piwicode/bandoneon/datasheets/CM-M1-6-M2-M2-5-M3-figur-M5-M6-M8-304-A2-70-En-Acier.jpg_.webp

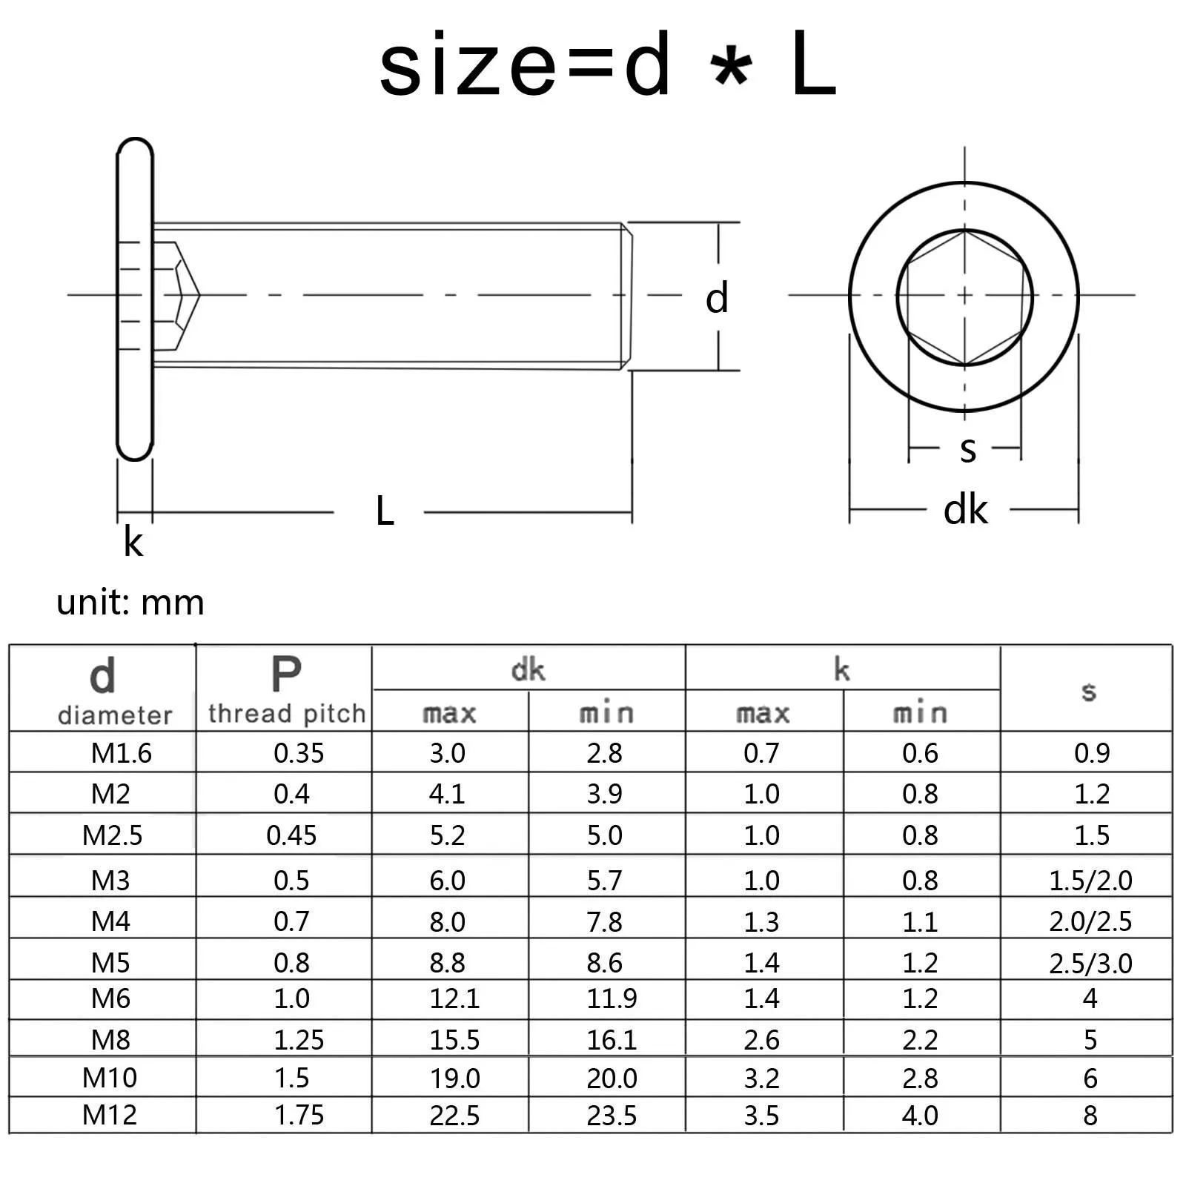
datasheets/CM-M1-6-M2-M2-5-M3-figur-M5-M6-M8-304-A2-70-En-Acier.jpg_.webp
