piwicode/bandoneon/datasheets/jack.webp

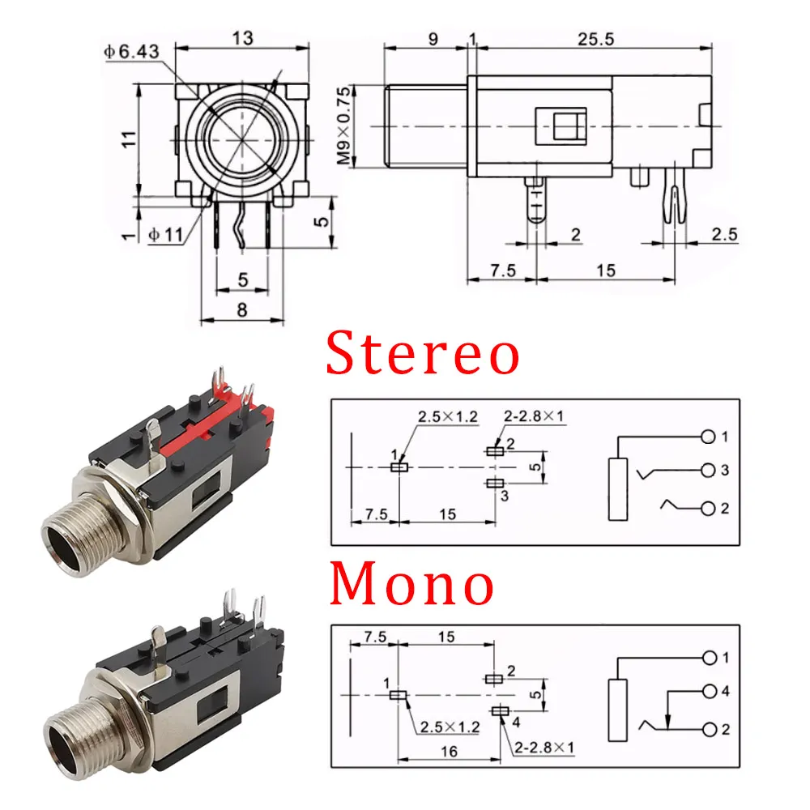
datasheets/jack.webp
