piwicode/bandoneon/images/Screenshot 2024-01-19 135625.png

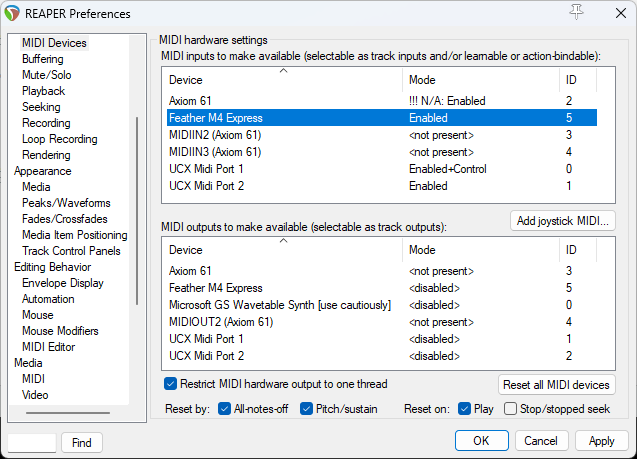
images/Screenshot 2024-01-19 135625.png
