piwicode/bandoneon/images/Screenshot 2024-01-19 135826.png

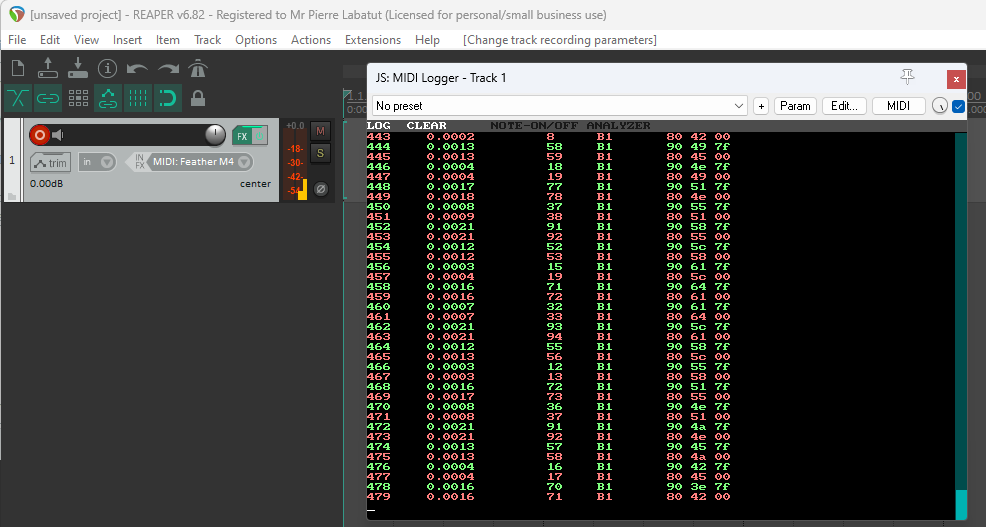
images/Screenshot 2024-01-19 135826.png
