piwicode/bandoneon/images/Screenshot 2024-01-19 183334.png

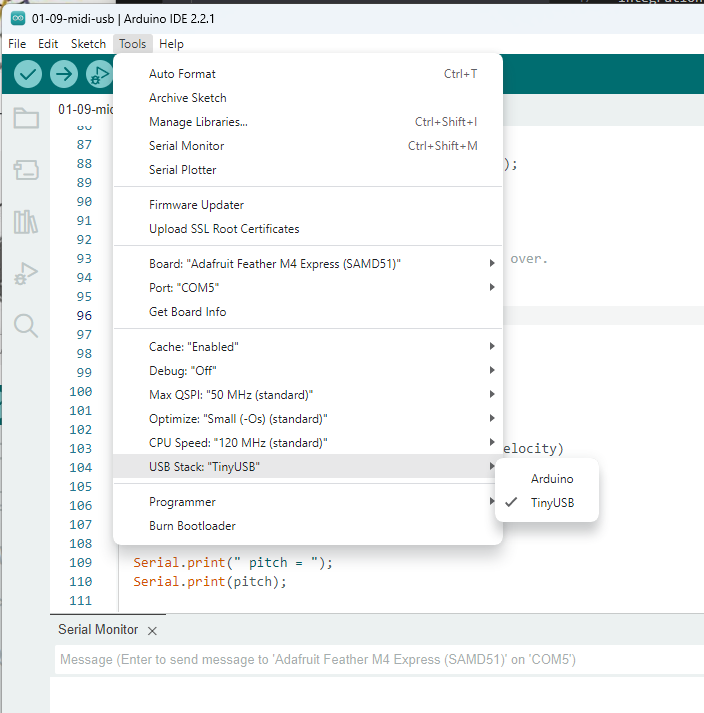
images/Screenshot 2024-01-19 183334.png
