piwicode/bandoneon/images/Screenshot 2024-01-19 212708.jpg

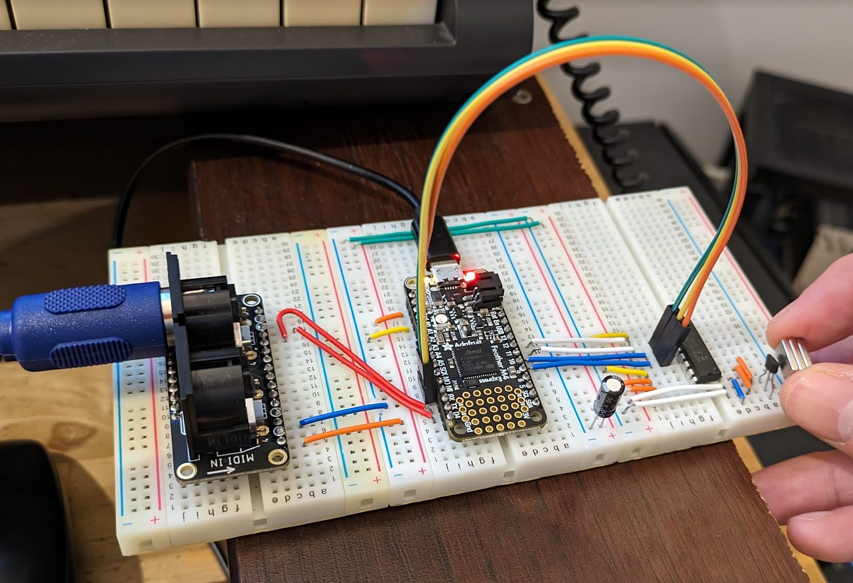
images/Screenshot 2024-01-19 212708.jpg
