piwicode/bandoneon/images/Screenshot 2024-01-24 084300.png

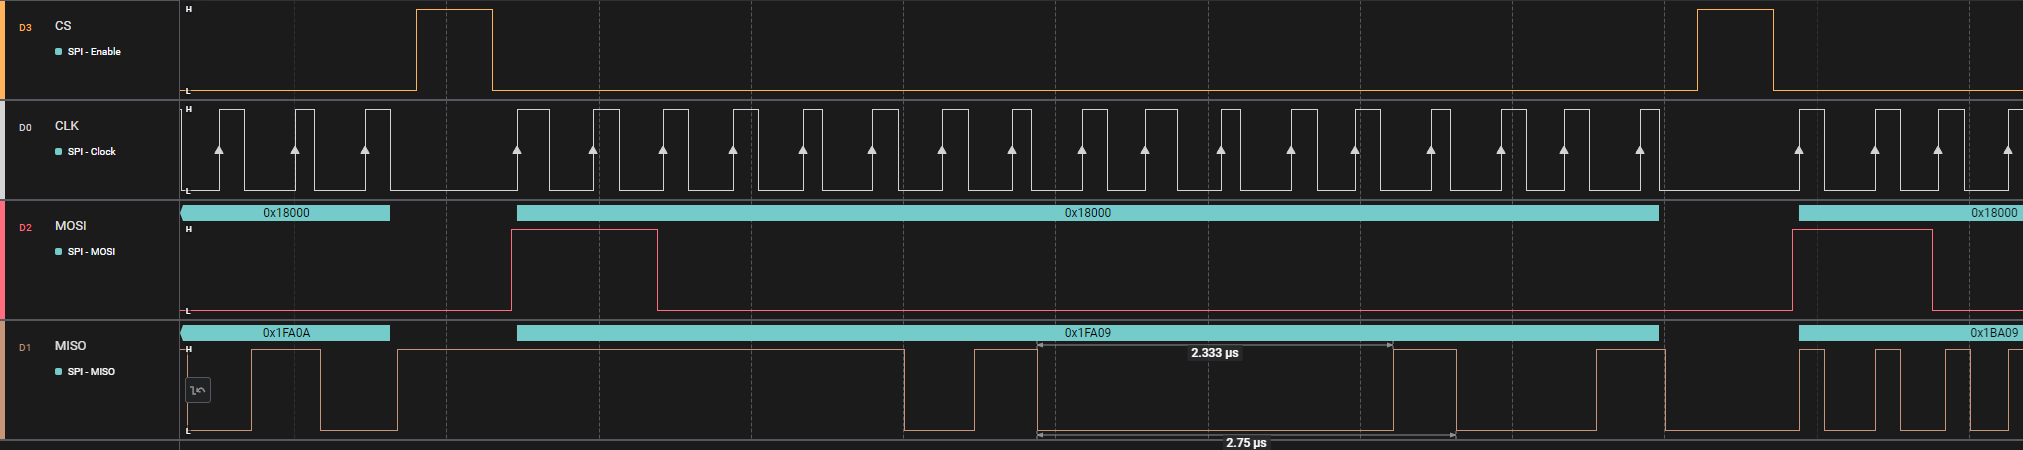
images/Screenshot 2024-01-24 084300.png
