piwicode/bandoneon/images/Screenshot 2024-01-25 232503.png

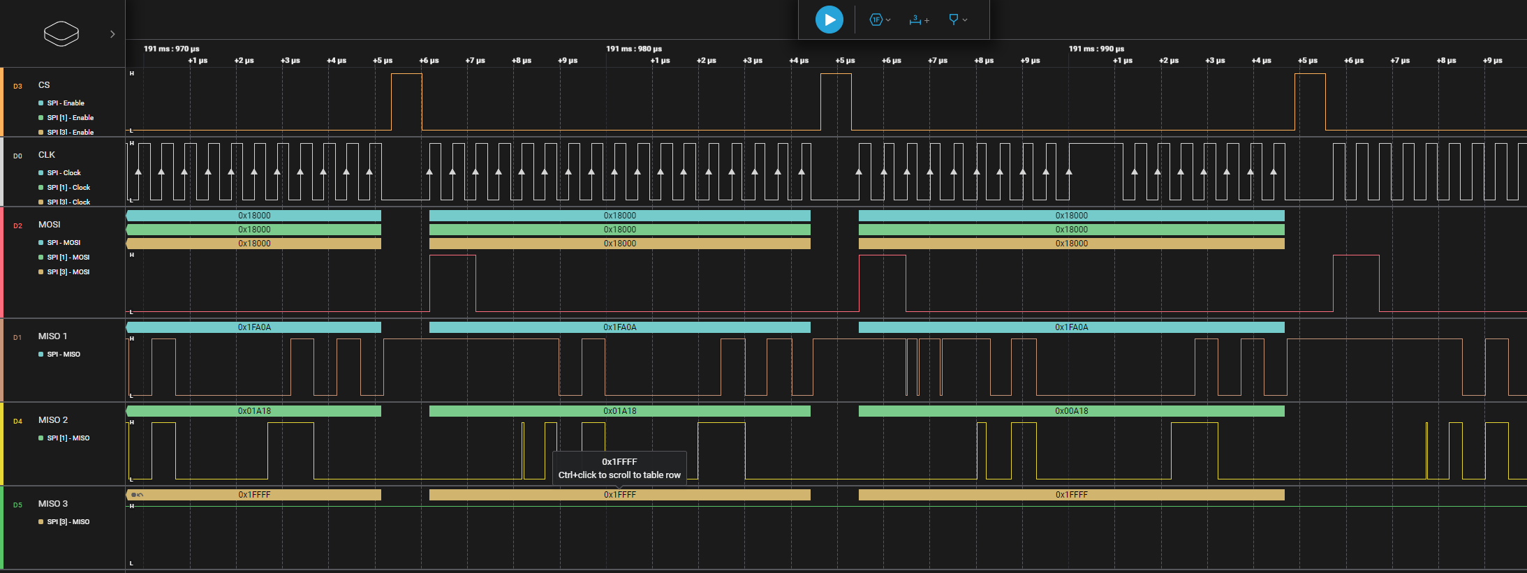
images/Screenshot 2024-01-25 232503.png
