piwicode/bandoneon/images/Screenshot 2024-01-27 221911.png

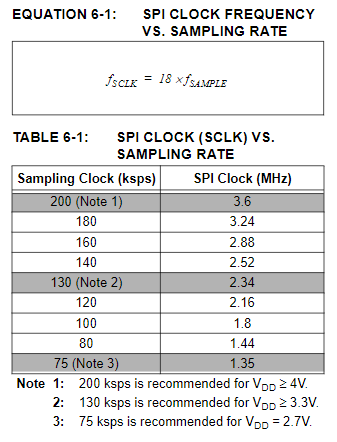
images/Screenshot 2024-01-27 221911.png
