piwicode/bandoneon/images/Screenshot 2024-01-31 140824.png

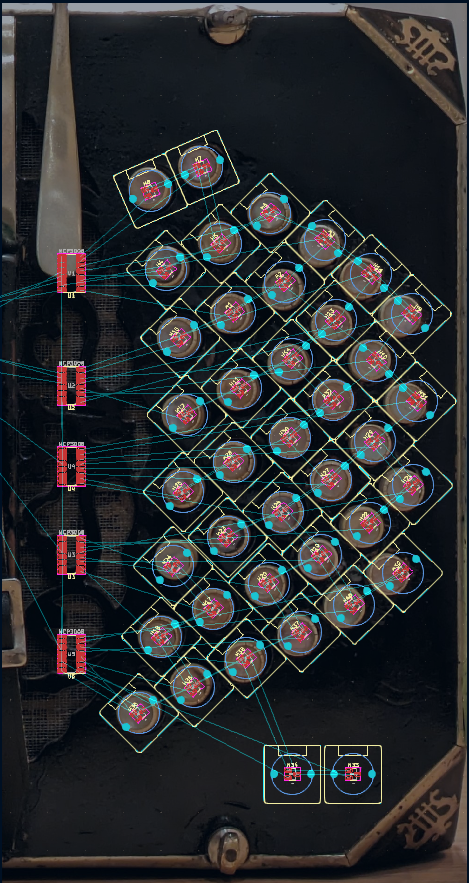
images/Screenshot 2024-01-31 140824.png
