piwicode/bandoneon/images/Screenshot 2024-01-31 140842.png

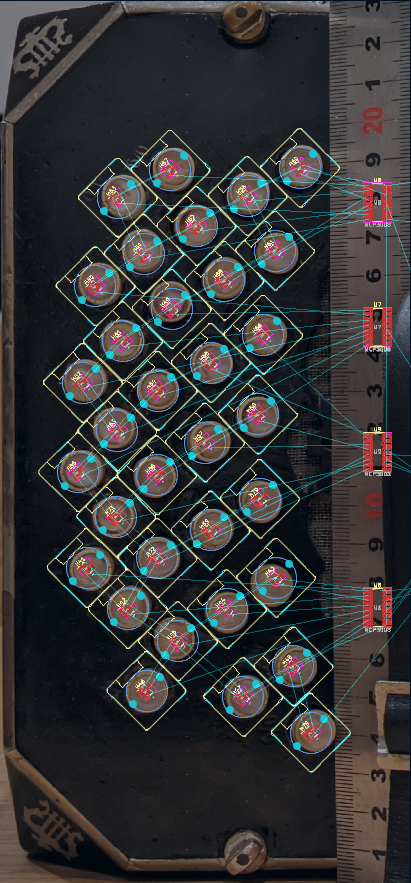
images/Screenshot 2024-01-31 140842.png
