piwicode/bandoneon/images/Screenshot 2024-01-31 201740.png

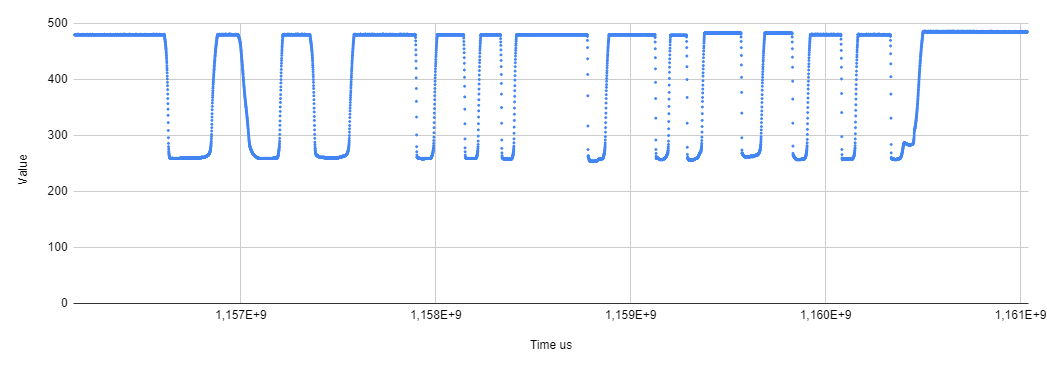
images/Screenshot 2024-01-31 201740.png
