piwicode/bandoneon/images/Screenshot 2024-02-16 172553.png

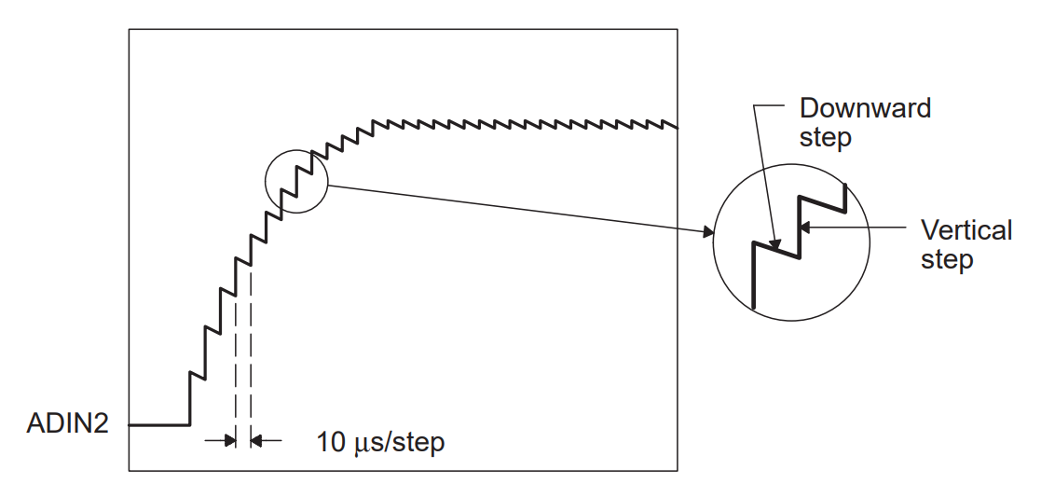
images/Screenshot 2024-02-16 172553.png
