piwicode/bandoneon/images/Screenshot 2024-02-16 174339.png

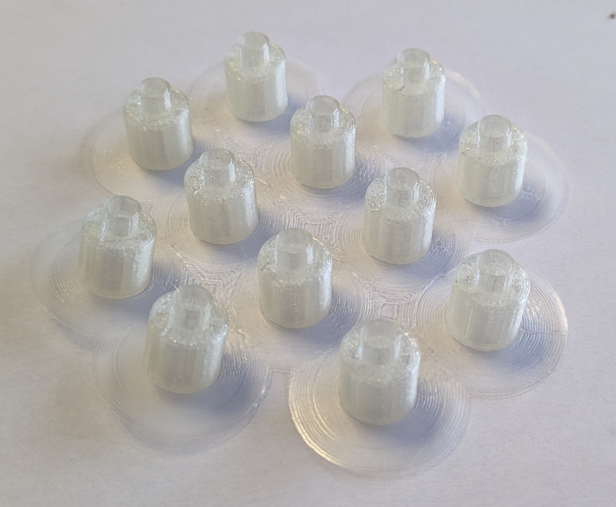
images/Screenshot 2024-02-16 174339.png
