piwicode/bandoneon/images/Screenshot 2024-02-16 190442.png

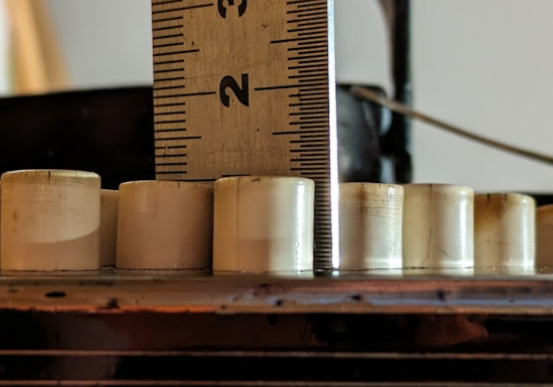
images/Screenshot 2024-02-16 190442.png
