piwicode/bandoneon/images/Screenshot 2024-02-16 225610.png

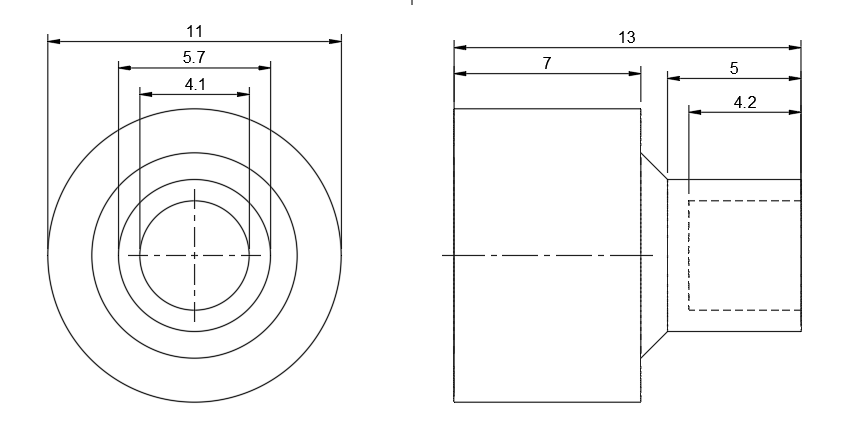
images/Screenshot 2024-02-16 225610.png
