piwicode/bandoneon/images/Screenshot 2024-02-16 225720.png

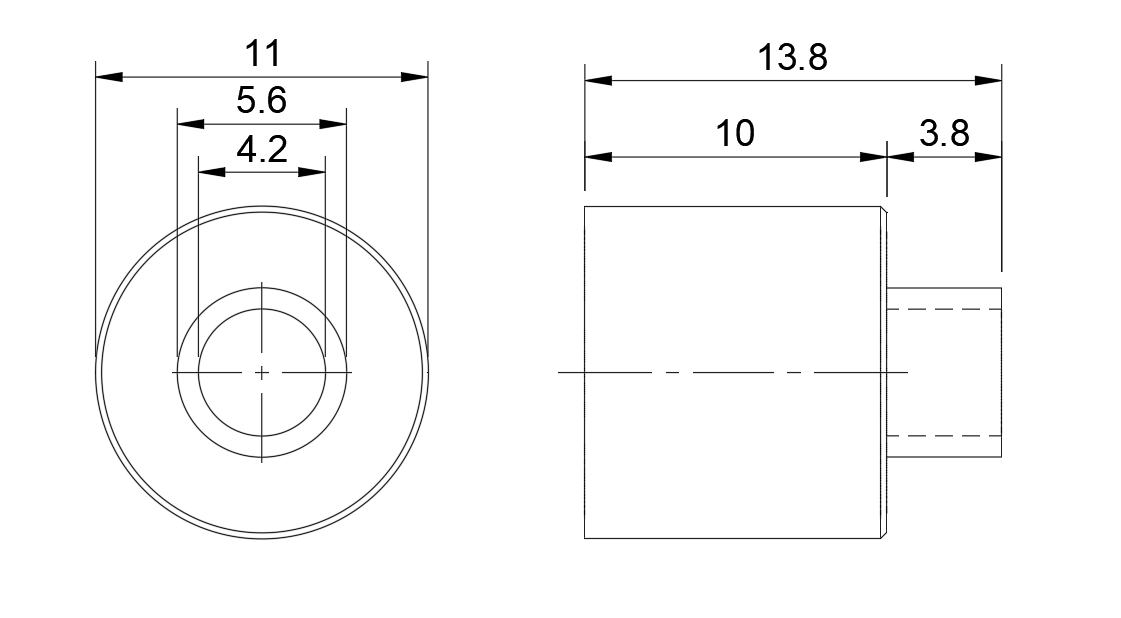
images/Screenshot 2024-02-16 225720.png
