piwicode/bandoneon/images/Screenshot 2024-02-16 230251.png

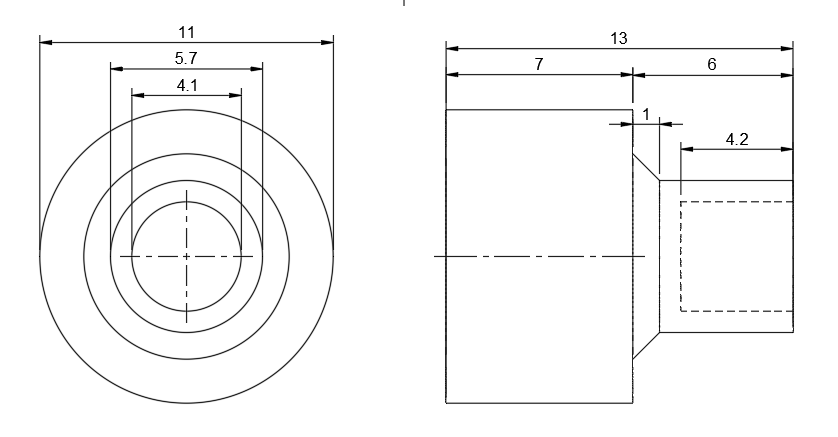
images/Screenshot 2024-02-16 230251.png
