piwicode/bandoneon/images/Screenshot 2024-03-01 095530.png

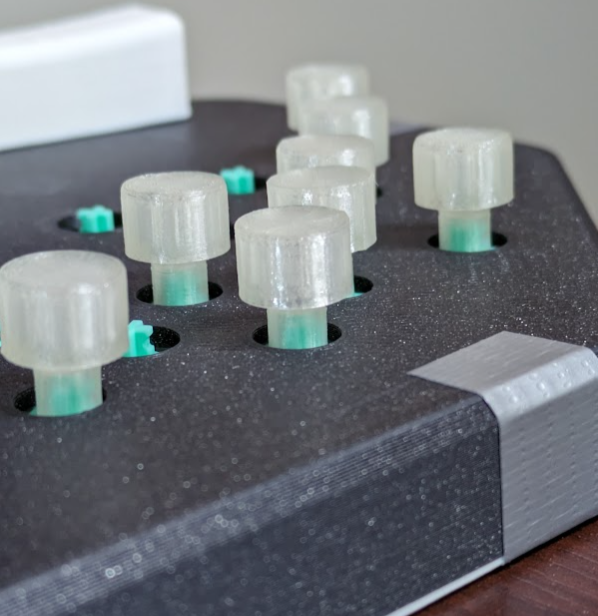
images/Screenshot 2024-03-01 095530.png
