piwicode/bandoneon/images/Screenshot 2024-03-01 095839.png

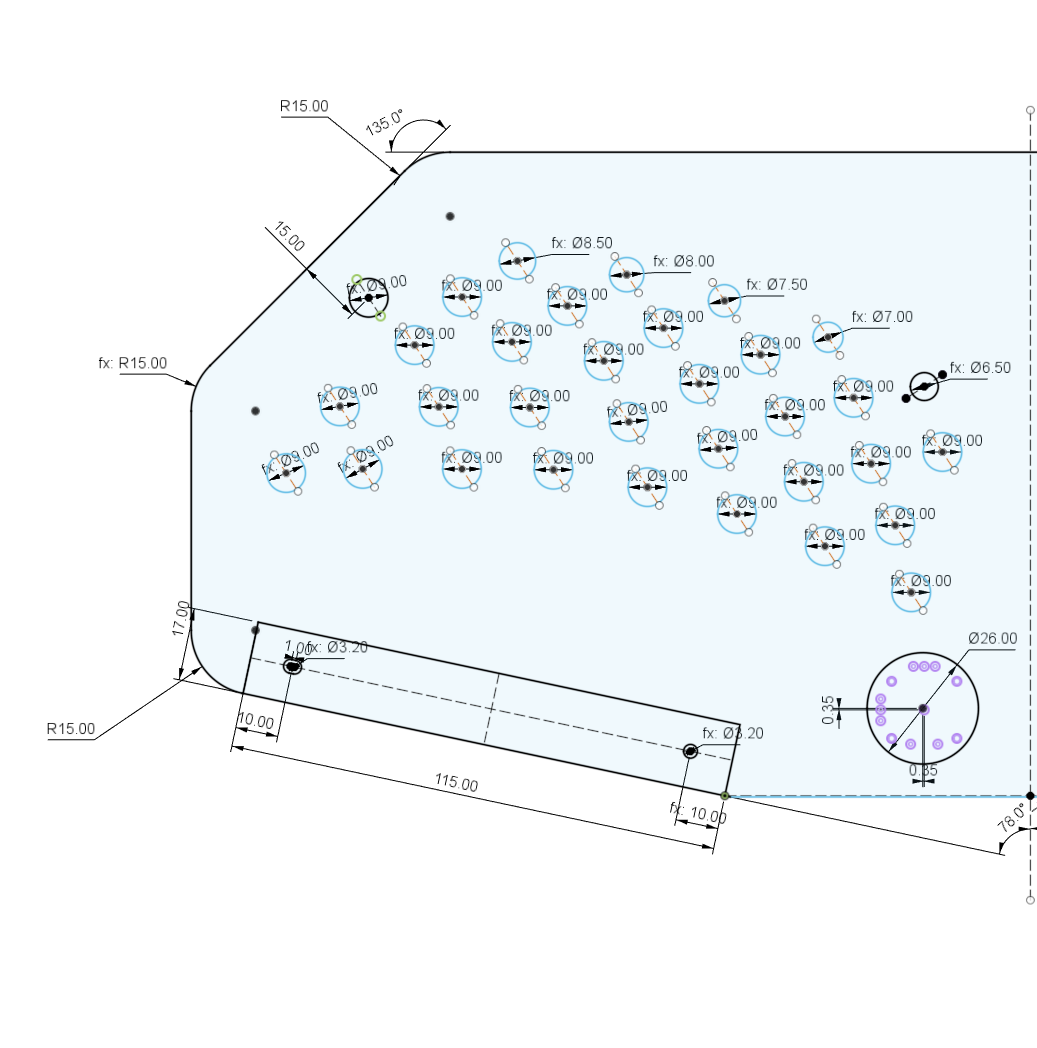
images/Screenshot 2024-03-01 095839.png
