piwicode/bandoneon/images/Screenshot 2024-04-13 213430.png

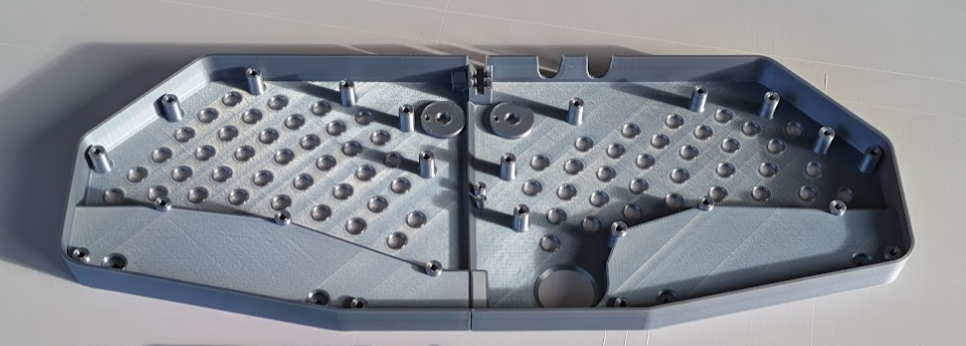
images/Screenshot 2024-04-13 213430.png
