piwicode/bandoneon/images/Screenshot 2024-04-13 214124.png

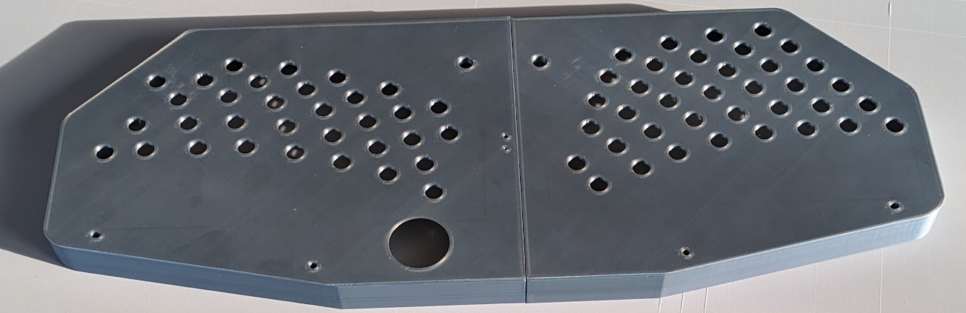
images/Screenshot 2024-04-13 214124.png
