piwicode/bandoneon/images/Screenshot 2024-04-13 214628.png

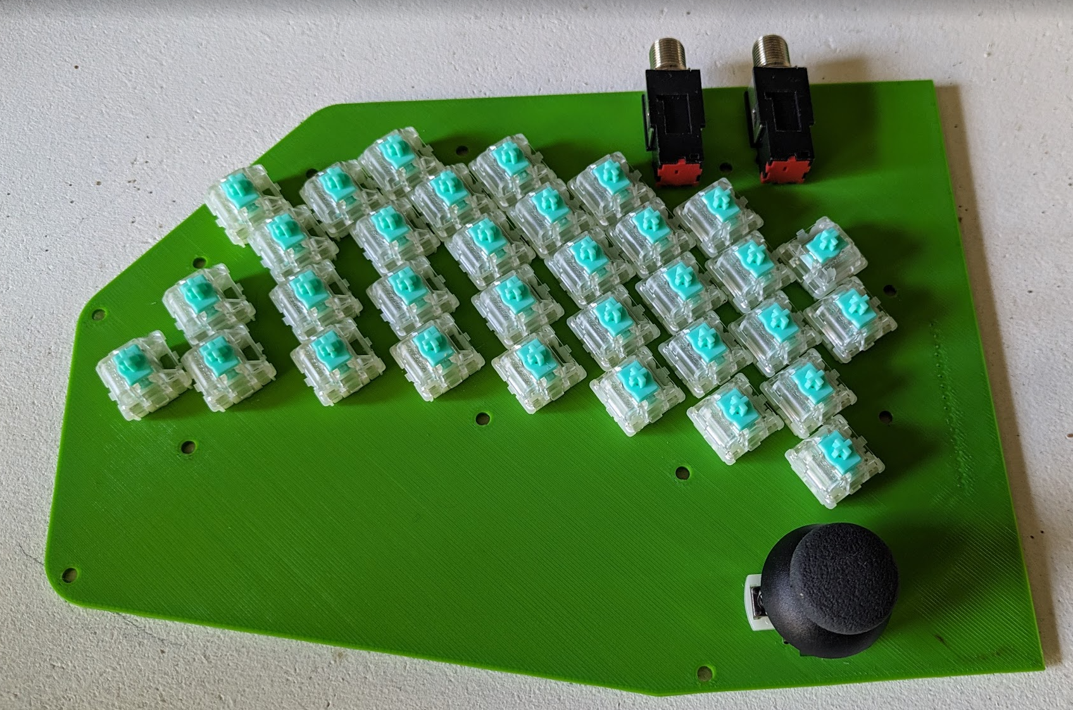
images/Screenshot 2024-04-13 214628.png
