piwicode/bandoneon/images/Screenshot from 2024-02-16 18-17-40.png

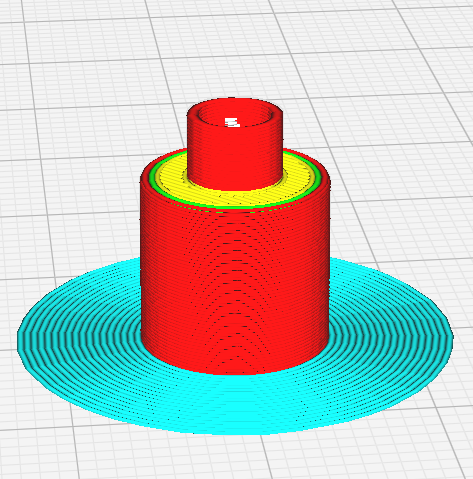
images/Screenshot from 2024-02-16 18-17-40.png
