piwicode/bandoneon/layout/half_left_side.jpg

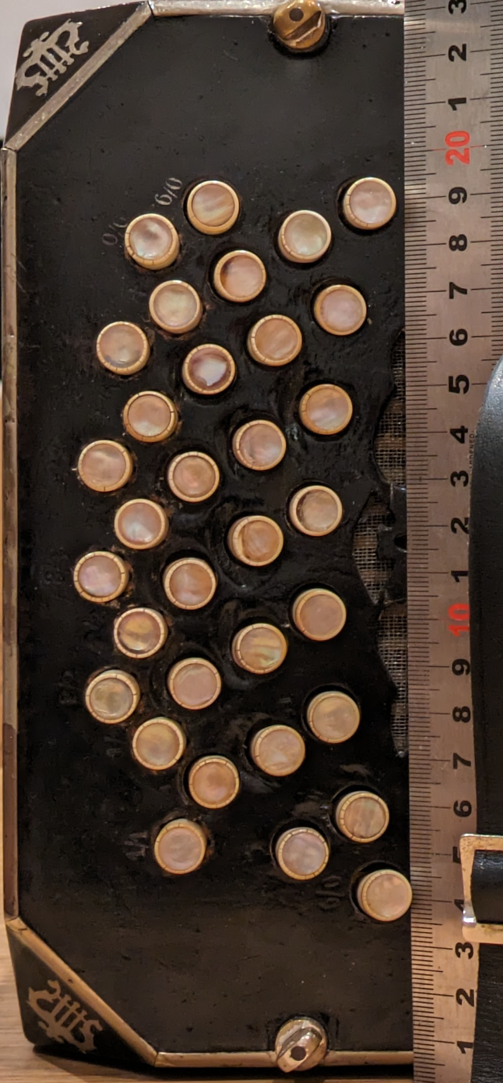
layout/half_left_side.jpg
