piwicode/bandoneon/layout/half_right_side.jpg

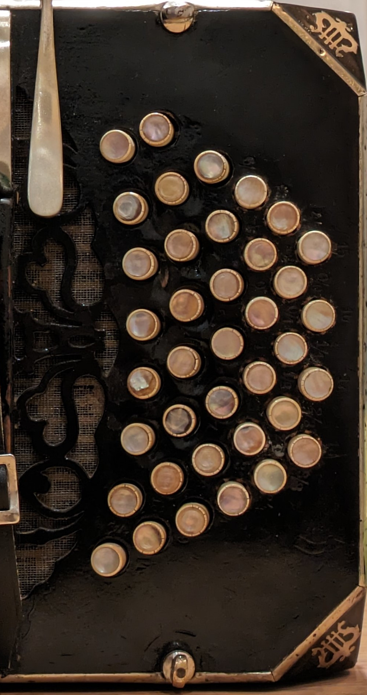
layout/half_right_side.jpg
