piwicode/bandoneon/layout/left_side.jpg

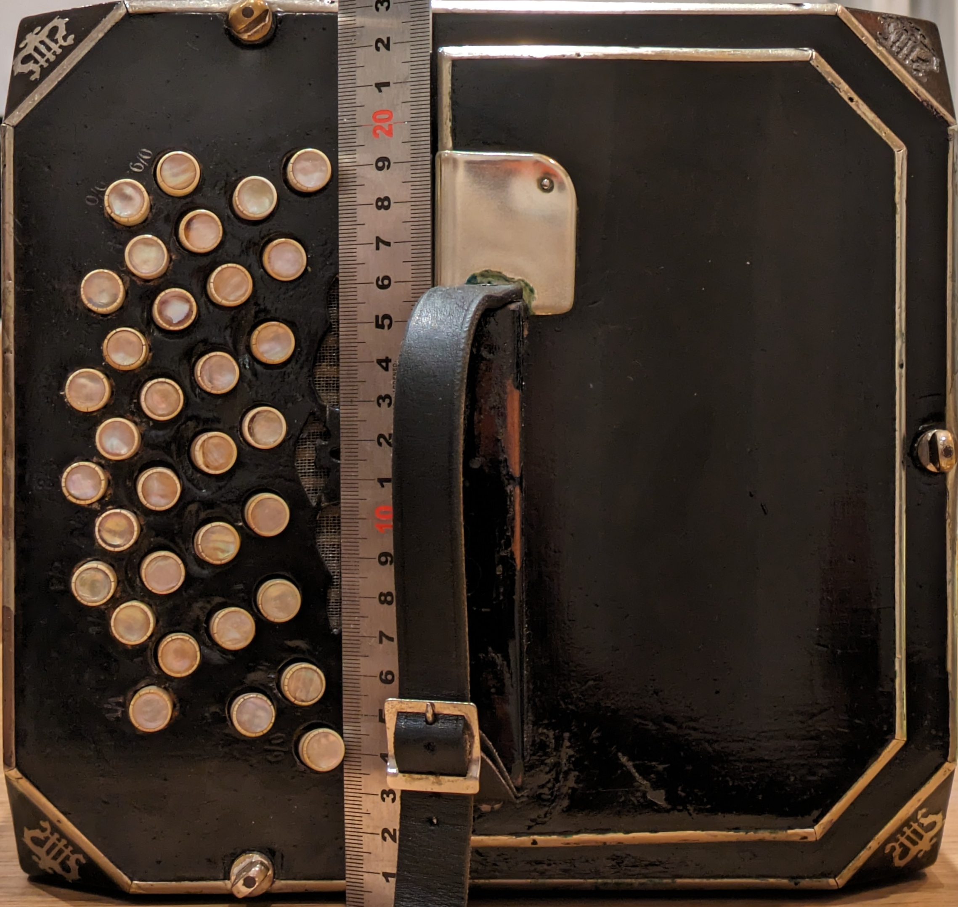
layout/left_side.jpg
