piwicode/bandoneon/layout/right_side.jpg

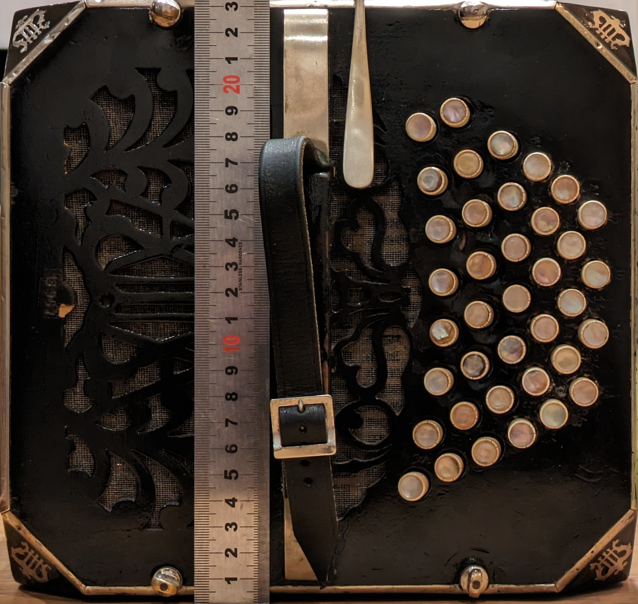
layout/right_side.jpg
