piwicode/bandoneon/stl/PCB R.stl

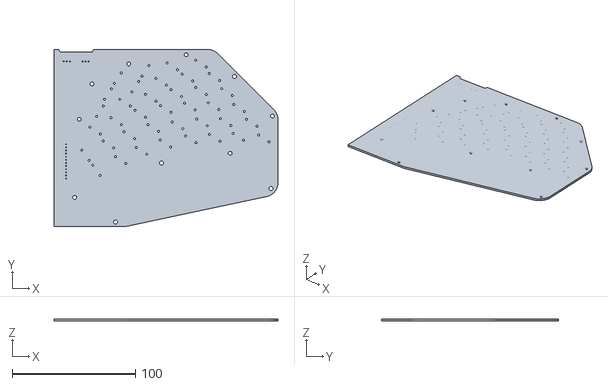
[picture p52: CAD file, 2024-03-18]
stl/PCB R.stl
182.0 x 143.8 x 1.60
