piwicode/bandoneon/boards/bandoneon/bandoneon.kicad_sch

## KiCad design boards/bandoneon/bandoneon.kicad_sch (2024-03-30)

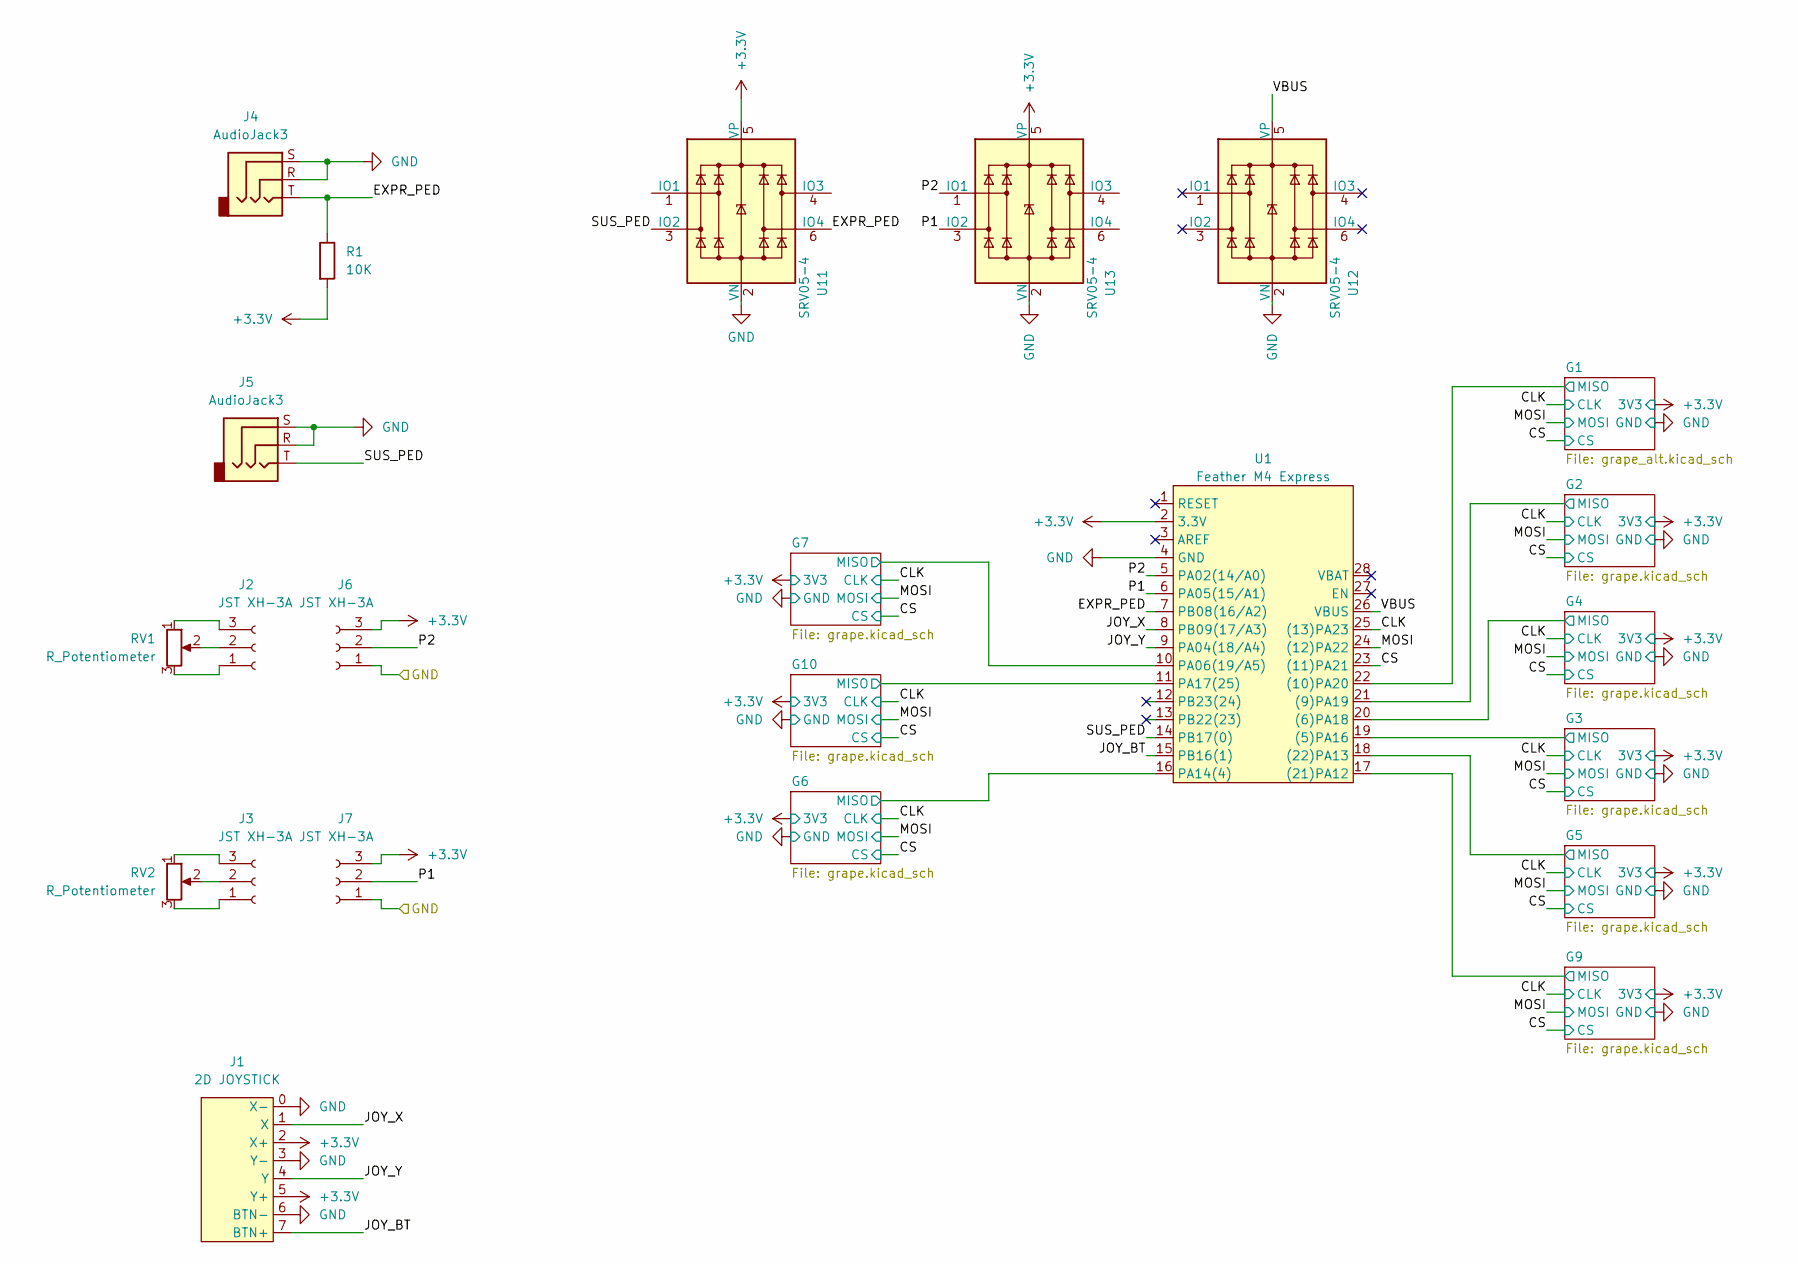
[picture p54: schematic bandoneon.kicad_sch]

Parts:
J1: 2D JOYSTICK; Adafruit (512) Analog 2-axis Thumb Joystick with Select But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
J2, J3: JST XH-3A
J4, J5: AudioJack3; Jack TRS
J6, J7: JST XH-3A; JST_XH_B3B-XH-A_1x03_P2.50mm_Vertical
R1: 10K; R_0603_1608Metric; LCSC Part C25804
RV1, RV2: R_Potentiometer
U1: Feather M4 Express; Adafruit_Feather_M4_Express
U11, U12, U13: SRV05-4; SOT-23-6; LCSC Part C2836319

Connections:
+3.3V: J1.2 (X+), J1.5 (Y+), J6.3, J7.3, R1.2, U1.2 (3.3V), U11.5 (VP), U13.5 (VP)
CLK: U1.25 ((13)PA23)
CS: U1.23 ((11)PA21)
EXPR_PED: J4.T, R1.1, U1.7 (PB08(16/A2)), U11.6 (IO4)
GND: J1.0 (X-), J1.3 (Y-), J1.6 (BTN-), J4.R, J4.S, J5.R, J5.S, J6.1, J7.1, U1.4 (GND), U11.2 (VN), U12.2 (VN), U13.2 (VN)
JOY_BT: J1.7 (BTN+), U1.15 (PB16(1))
JOY_X: J1.1 (X), U1.8 (PB09(17/A3))
JOY_Y: J1.4 (Y), U1.9 (PA04(18/A4))
MISO: U1.10 (PA06(19/A5)), U1.11 (PA17(25)), U1.16 (PA14(4)), U1.17 ((21)PA12), U1.18 ((22)PA13), U1.19 ((5)PA16), U1.20 ((6)PA18), U1.21 ((9)PA19), U1.22 ((10)PA20)
MOSI: U1.24 ((12)PA22)
unnamed: J2.1, RV1.3
unnamed: J2.2, RV1.2
unnamed: J2.3, RV1.1
unnamed: J3.1, RV2.3
unnamed: J3.2, RV2.2
unnamed: J3.3, RV2.1
P1: J7.2, U1.6 (PA05(15/A1)), U13.3 (IO2)
P2: J6.2, U1.5 (PA02(14/A0)), U13.1 (IO1)
SUS_PED: J5.T, U1.14 (PB17(0)), U11.3 (IO2)
VBUS: U1.26 (VBUS), U12.5 (VP)
