piwicode/bandoneon/boards/bandoneon/grape.kicad_sch

## KiCad design boards/bandoneon/grape.kicad_sch (2024-03-27)

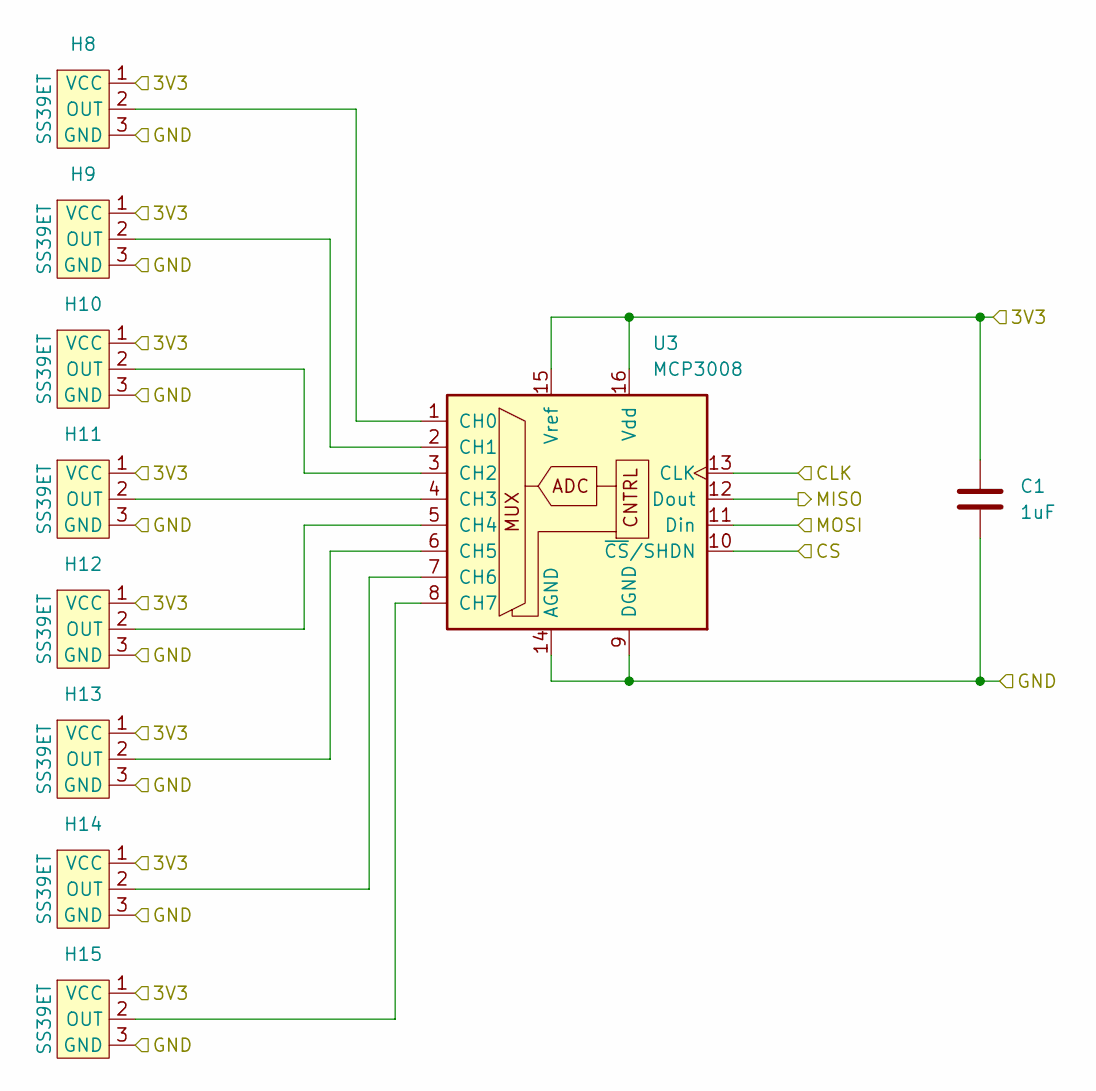
[picture p55: schematic grape.kicad_sch]

Parts:
C1: 1uF; C_0402_1005Metric; LCSC Part C52923
H8, H9, H10, H11, H12, H13, H14, H15: SS39ET; SOT-23_SS39ET; LCSC Part C126669
U3: MCP3008; SOIC-16_MCP3008T-I_SL; LCSC Part C1520159

Connections:
3V3: C1.1, H8.1 (VCC), H9.1 (VCC), H10.1 (VCC), H11.1 (VCC), H12.1 (VCC), H13.1 (VCC), H14.1 (VCC), H15.1 (VCC), U3.15 (Vref), U3.16 (Vdd)
CLK: U3.13 (CLK)
CS: U3.10 (~CS/SHDN)
GND: C1.2, H8.3 (GND), H9.3 (GND), H10.3 (GND), H11.3 (GND), H12.3 (GND), H13.3 (GND), H14.3 (GND), H15.3 (GND), U3.9 (DGND), U3.14 (AGND)
MISO: U3.12 (Dout)
MOSI: U3.11 (Din)
unnamed: H8.2 (OUT), U3.1 (CH0)
unnamed: H9.2 (OUT), U3.2 (CH1)
unnamed: H10.2 (OUT), U3.3 (CH2)
unnamed: H11.2 (OUT), U3.4 (CH3)
unnamed: H12.2 (OUT), U3.5 (CH4)
unnamed: H13.2 (OUT), U3.6 (CH5)
unnamed: H14.2 (OUT), U3.7 (CH6)
unnamed: H15.2 (OUT), U3.8 (CH7)
