piwicode/bandoneon/boards/bandoneon/grape_alt.kicad_sch

## KiCad design boards/bandoneon/grape_alt.kicad_sch (2024-03-27)

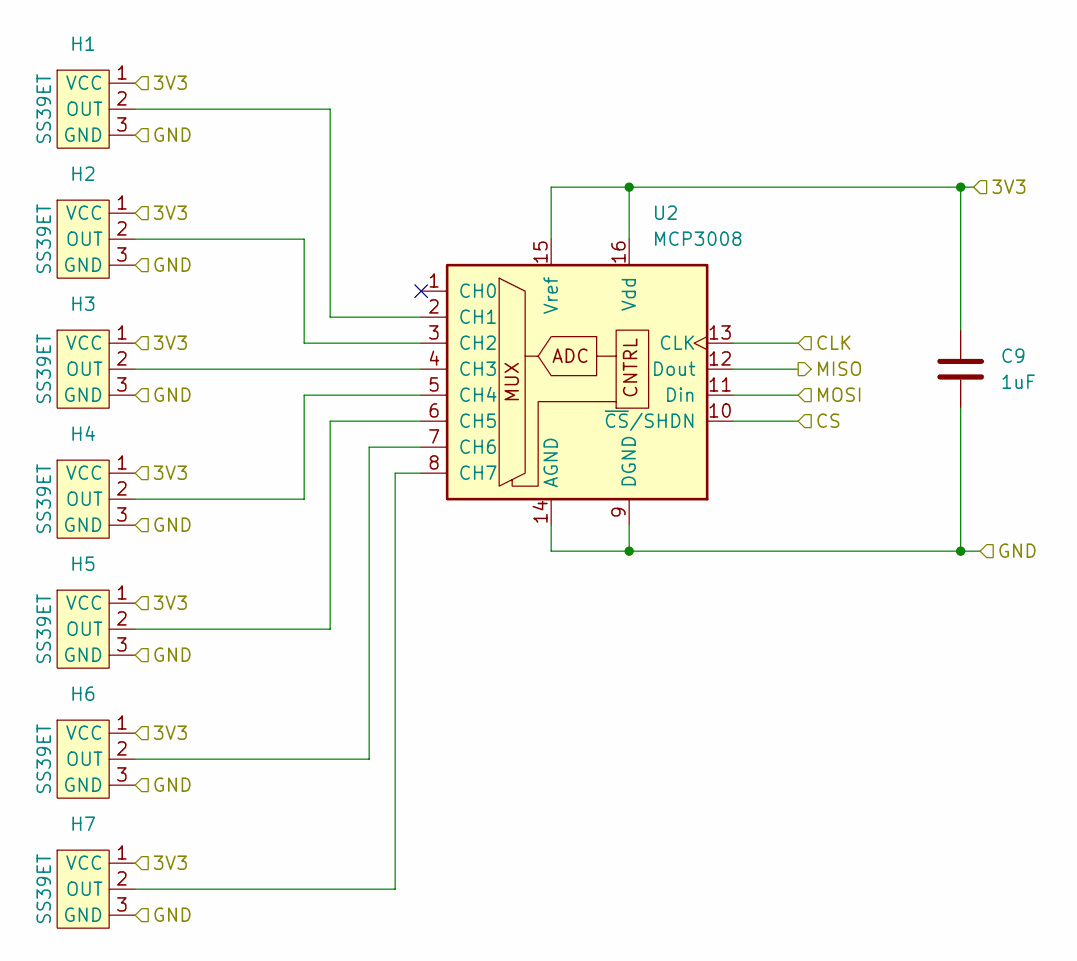
[picture p56: schematic grape_alt.kicad_sch]

Parts:
C9: 1uF; C_0402_1005Metric; LCSC Part C52923
H1, H2, H3, H4, H5, H6, H7: SS39ET; SOT-23_SS39ET; LCSC Part C126669
U2: MCP3008; SOIC-16_MCP3008T-I_SL; LCSC Part C1520159

Connections:
3V3: C9.1, H1.1 (VCC), H2.1 (VCC), H3.1 (VCC), H4.1 (VCC), H5.1 (VCC), H6.1 (VCC), H7.1 (VCC), U2.15 (Vref), U2.16 (Vdd)
CLK: U2.13 (CLK)
CS: U2.10 (~CS/SHDN)
GND: C9.2, H1.3 (GND), H2.3 (GND), H3.3 (GND), H4.3 (GND), H5.3 (GND), H6.3 (GND), H7.3 (GND), U2.9 (DGND), U2.14 (AGND)
MISO: U2.12 (Dout)
MOSI: U2.11 (Din)
unnamed: H1.2 (OUT), U2.2 (CH1)
unnamed: H2.2 (OUT), U2.3 (CH2)
unnamed: H3.2 (OUT), U2.4 (CH3)
unnamed: H4.2 (OUT), U2.5 (CH4)
unnamed: H5.2 (OUT), U2.6 (CH5)
unnamed: H6.2 (OUT), U2.7 (CH6)
unnamed: H7.2 (OUT), U2.8 (CH7)
